braineniac/garry/kicad/garry/garry.kicad_pcb

## KiCad design KiCAD/PC8001extRS232.sch

Schematic: PC8001extRS232.sch

Parts:
C1, C2, C3, C4, C5, C6, C7, C8, C9, C10: 0.1u
C11, C12: 22p
J1: PC8001 Ext Con
J2: 232C JP
J3: 232C-1
J4: 232C-2
R1, R2: 10k
R3: 1M
RN1, RN2: 10k; R_Array_SIP9
U1, U5: 74LS04
U2: 74LS148
U3: 74LS541
U4, U7: 74LS32
U6: 74LS30
U8, U9: 8251
U10: 74HC4060
Y1: 19.6608MHZ

Notes on the sheet:
GND
CTS
+5V
TxD
RxD
RTS
